e2002/KaRC/src/KaRC/HX1230Fonts.h

#ifndef HX1230Fonts_h
#define HX1230Fonts_h

const uint8_t HX1230RUS[] PROGMEM =
{
-8, 16, 32, 255,   // -width, height, firstChar, lastChar
        0x04, 0x00, 0x00, 0x00, 0x00, 0x00, 0x00, 0x00, 0x00, 0x00, 0x00, 0x00, 0x00, 0x00, 0x00, 0x00, 0x00,  //  
        0x04, 0x3E, 0x00, 0xFF, 0x33, 0xFF, 0x33, 0x3E, 0x00, 0x00, 0x00, 0x00, 0x00, 0x00, 0x00, 0x00, 0x00,  // !
        0x05, 0x07, 0x00, 0x07, 0x00, 0x00, 0x00, 0x00, 0x00, 0x07, 0x00, 0x07, 0x00, 0x00, 0x00, 0x00, 0x00,  // "
        0x07, 0x20, 0x01, 0xFE, 0x1F, 0xFE, 0x1F, 0x20, 0x01, 0xFE, 0x1F, 0xFE, 0x1F, 0x20, 0x01, 0x00, 0x00,  // #
        0x07, 0x38, 0x06, 0x3C, 0x0E, 0x64, 0x08, 0xFF, 0x3F, 0xFF, 0x3F, 0x84, 0x09, 0x18, 0x07, 0x00, 0x00,  // $
        0x07, 0x1E, 0x30, 0x33, 0x1C, 0x1E, 0x07, 0xC0, 0x01, 0x70, 0x1E, 0x1C, 0x33, 0x07, 0x1E, 0x00, 0x00,  // %
        0x07, 0x1E, 0x1F, 0xF3, 0x31, 0xE1, 0x20, 0xB3, 0x31, 0x1E, 0x1F, 0x00, 0x1B, 0x80, 0x31, 0x00, 0x00,  // &
        0x02, 0x0B, 0x00, 0x07, 0x00, 0x00, 0x00, 0x00, 0x00, 0x00, 0x00, 0x00, 0x00, 0x00, 0x00, 0x00, 0x00,  // '
        0x04, 0xF0, 0x07, 0xFE, 0x3F, 0x0F, 0x78, 0x01, 0x40, 0x00, 0x00, 0x00, 0x00, 0x00, 0x00, 0x00, 0x00,  // (
        0x04, 0x01, 0x40, 0x0F, 0x78, 0xFE, 0x3F, 0xF0, 0x07, 0x00, 0x00, 0x00, 0x00, 0x00, 0x00, 0x00, 0x00,  // )
        0x07, 0x80, 0x00, 0xA0, 0x02, 0xE0, 0x03, 0xC0, 0x01, 0xE0, 0x03, 0xA0, 0x02, 0x80, 0x00, 0x00, 0x00,  // *
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
0xF0, 0xF0, 0xF0, 0xF0, 0xF0, 0xF0, 0xF0, 0xF0, 0xF0, 0xF0, 0xF0, 0xF0, 0xF0, 0xF0, 0xF0, 0xF0,   // 0x01D0 (464) pixels
0xF0, 0xF0, 0xF0, 0xF0, 0xF0, 0xF0, 0xF0, 0xF0, 0xF0, 0xF0, 0xF0, 0xF0, 0xF0, 0xF0, 0xF0, 0xF0,   // 0x01E0 (480) pixels
};
#endif
